xenomorphales/ceres/soft/v2017/robot_drivers/include/arm.hpp

#ifndef ARM_H
#define ARM_H

#include "singleton.hpp"
#include "service.hpp"

class Arm : public Singleton<Arm>, public Service {
private:
  class Left;
  class Right;

public:
  enum ArmState {
    ARM_DISABLED,
    ARM_RETRACTED,
    ARM_DEPLOYED,
    ARM_MOVING,
    ARM_ERROR
  };

  enum GripState {
    OPEN, CLOSE
  };

  enum GripHoldState {
    NONE, LEFT, RIGHT, BOTH
  };

public:
  Arm(void);

public:
  inline Left& left(void) { return *(Left*)this; }
  inline Right& right(void) { return *(Right*)this; }
};

class Arm::Left : private Arm {
private:
  class Grip;

public:
  void deploy(void);
  void retract(void);

public:
  void setAngles(float a1, float a2);

public:
  ArmState state(void);

public:
  inline Grip& grip(void) { return *(Grip*)this; }
};

class Arm::Left::Grip : private Arm {
public:
  void open(void);
  void close(void);

  GripHoldState hold(void);

public:
  GripState state(void);
};

class Arm::Right : private Arm {
private:
  class Grip;

public:
  void deploy(void);
  void retract(void);

public:
  void setAngles(float a1, float a2);

public:
  ArmState state(void);

public:
  inline Grip& grip(void) { return *(Grip*)this; }
};

class Arm::Right::Grip : private Arm {
public:
  void open(void);
  void close(void);

  GripHoldState hold(void);

public:
  GripState state(void);
};

#endif//ARM_H
