xenomorphales/ceres/soft/v2017/robot_drivers/include/pull.hpp

#ifndef PULL_H
#define PULL_H

#include "singleton.hpp"

class Pull : public Singleton<Pull> {
public:
  enum State {
    IN, OUT
  };

public:
  Pull(void);

public:
  State state(void);
};

#endif//PULL_H
